ImperialCollegeLondon/openFrame/openFrame CAD/OF-PP-SM30.stp

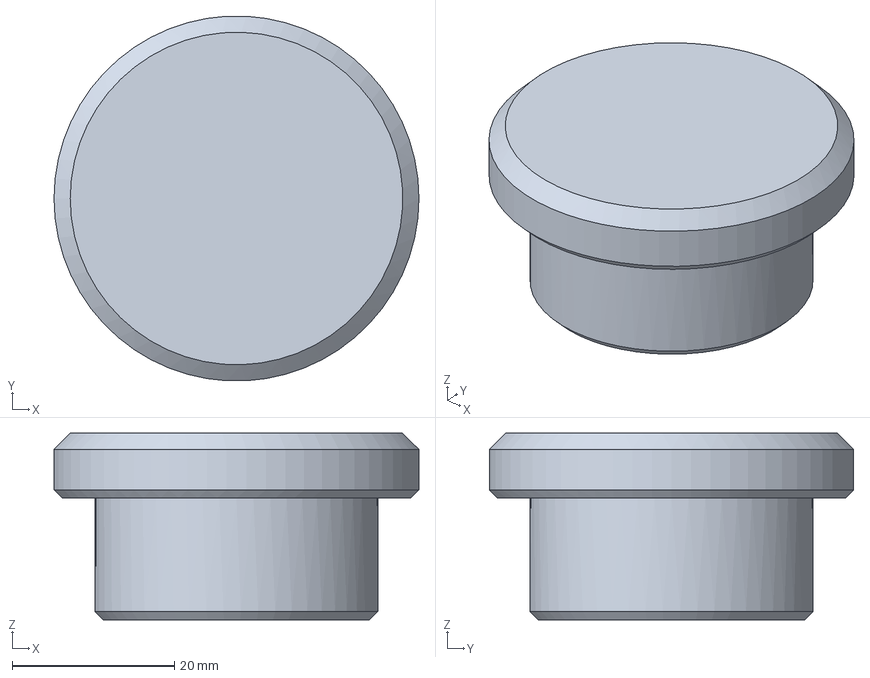
[picture p14: CAD file, 2023-07-18]
openFrame CAD/OF-PP-SM30.stp
45.0 x 44.9 x 23.0 mm
