ImperialCollegeLondon/openFrame/openFrame CAD/OF-AD-TI-ARM-LED-CAIRN.stp

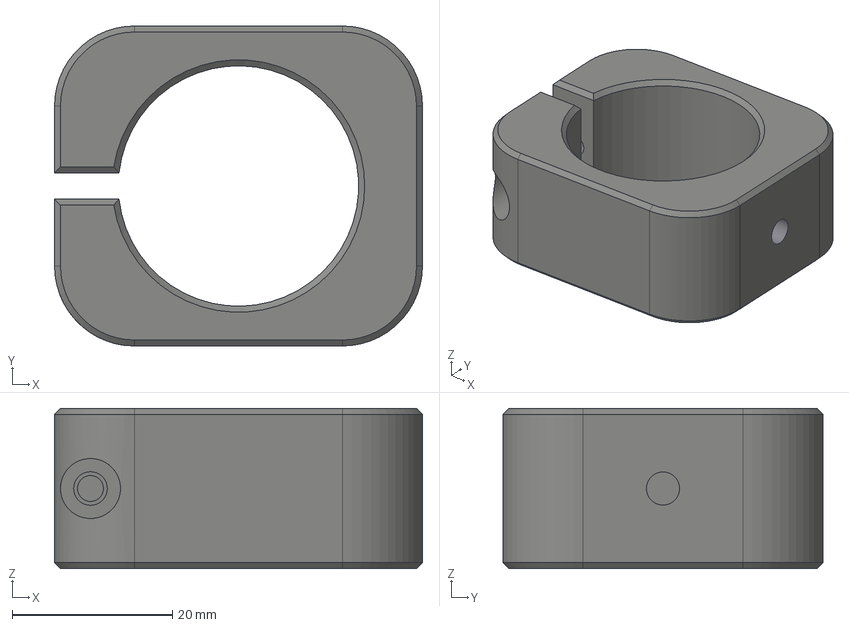
[picture p15: CAD file, 2023-07-18]
openFrame CAD/OF-AD-TI-ARM-LED-CAIRN.stp
46.0 x 40.0 x 20.0 mm
