ImperialCollegeLondon/openFrame/openFrame CAD/OF-AD-SM2-TL-OLYMPUS.stp

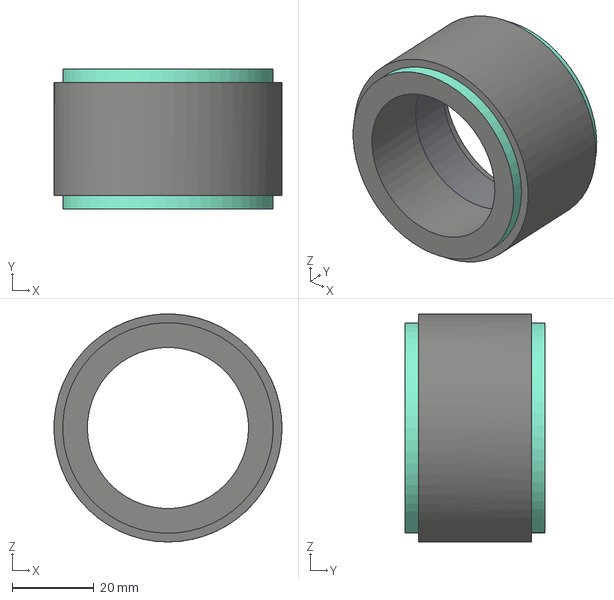
[picture p16: CAD file, 2023-07-18]
openFrame CAD/OF-AD-SM2-TL-OLYMPUS.stp
55.9 x 34.2 x 55.9 mm
