ImperialCollegeLondon/openFrame/openFrame CAD/OF-AD-LL-SM1.stp

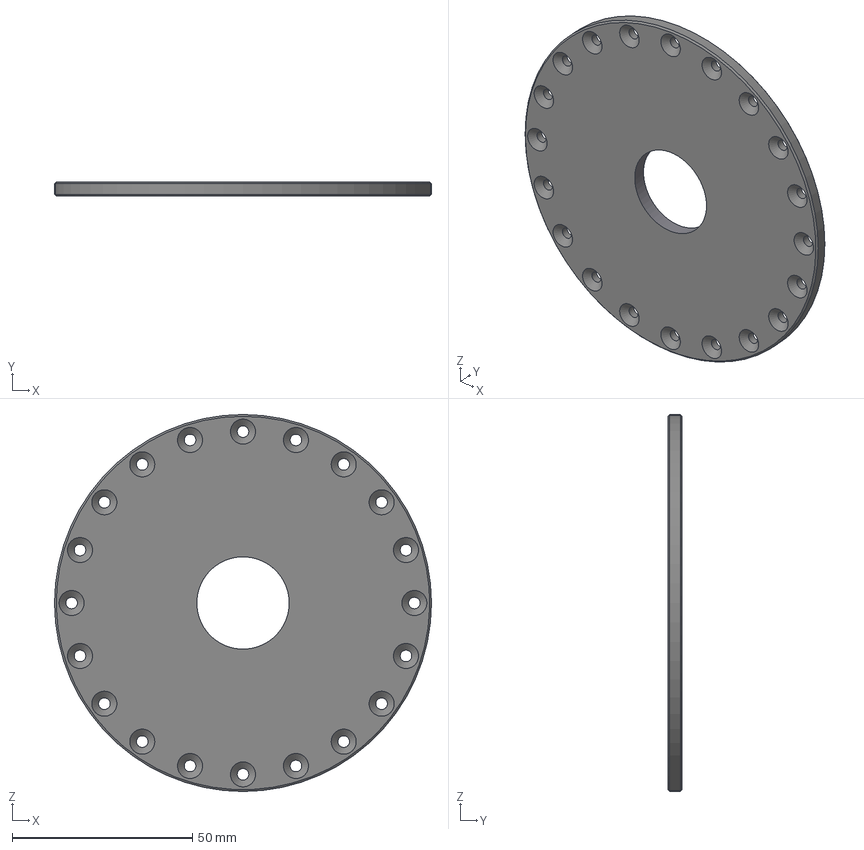
[picture p17: CAD file, 2023-07-18]
openFrame CAD/OF-AD-LL-SM1.stp
104.5 x 4.00 x 104.5 mm
