ImperialCollegeLondon/openFrame/openFrame CAD/OF-CL-SM2.stp

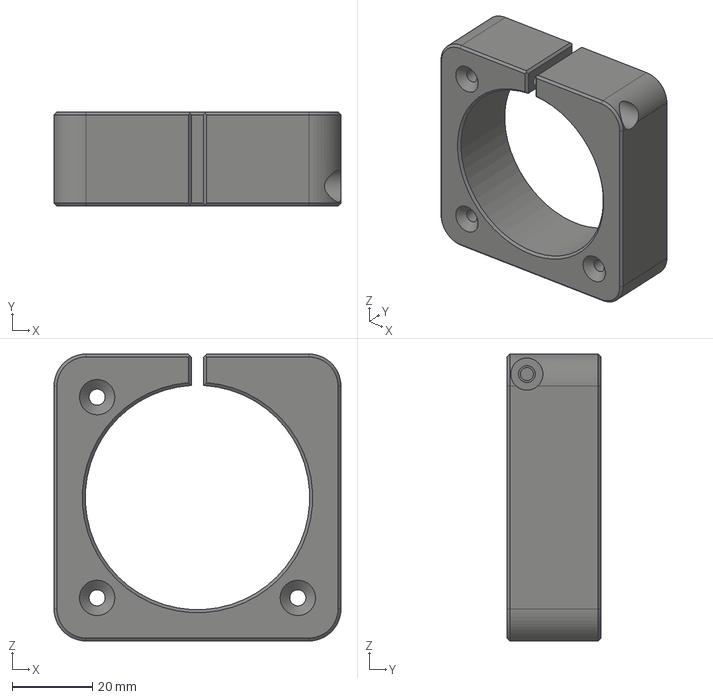
[picture p18: CAD file, 2023-07-18]
openFrame CAD/OF-CL-SM2.stp
71.5 x 23.5 x 71.5 mm
