ImperialCollegeLondon/openFrame/openFrame CAD/OF-PP-SM2.stp

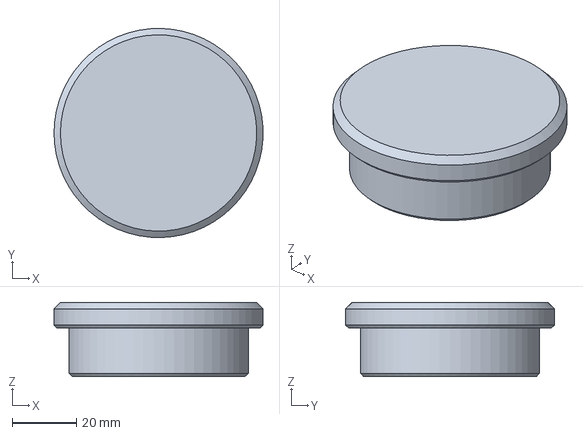
[picture p19: CAD file, 2023-07-18]
openFrame CAD/OF-PP-SM2.stp
65.0 x 65.0 x 23.0 mm
