ImperialCollegeLondon/openFrame/openFrame CAD/OF-LL-FL-MOT.stp

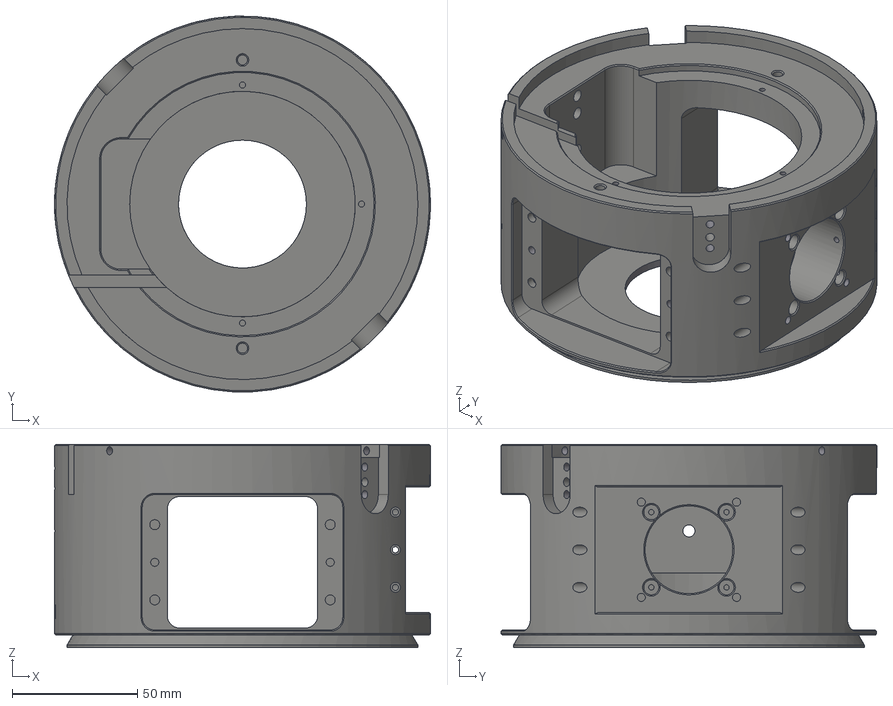
[picture p20: CAD file, 2023-07-18]
openFrame CAD/OF-LL-FL-MOT.stp
150.0 x 149.9 x 81.0 mm
