ImperialCollegeLondon/openFrame/openFrame CAD/OF-AD-OBH-RMS-45.stp

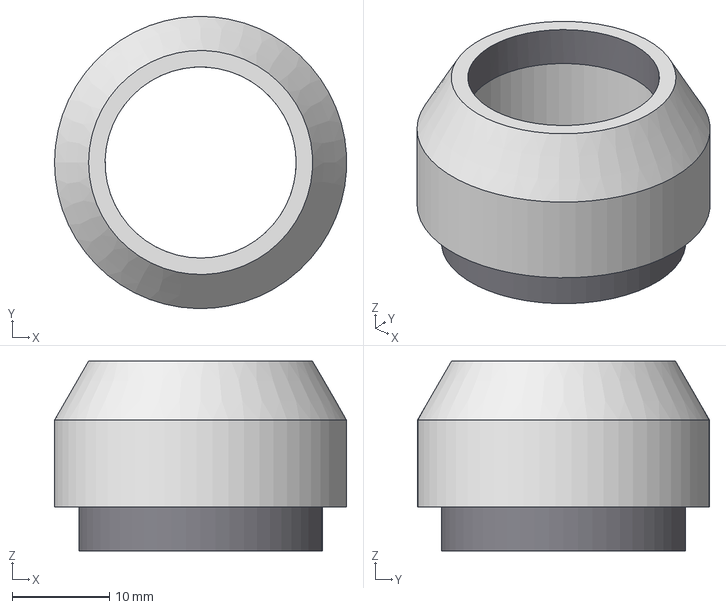
[picture p21: CAD file, 2023-07-18]
openFrame CAD/OF-AD-OBH-RMS-45.stp
30.0 x 30.0 x 19.5 mm
