ImperialCollegeLondon/openFrame/openFrame CAD/OF-LL-80.stp

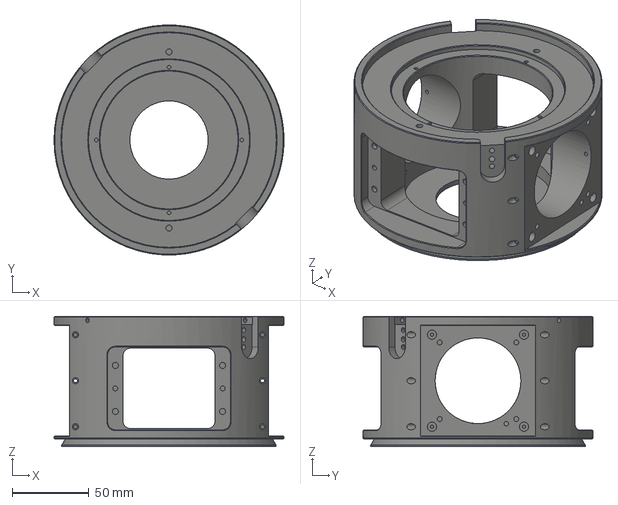
[picture p22: CAD file, 2023-07-18]
openFrame CAD/OF-LL-80.stp
150.0 x 149.9 x 85.0 mm
