ImperialCollegeLondon/openFrame/openFrame CAD/OF-IN-2P-OD.stp

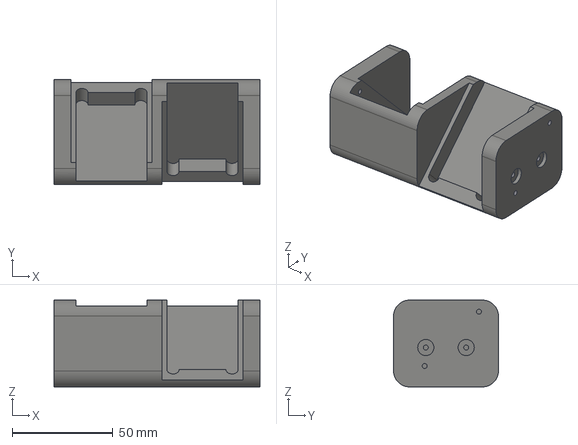
[picture p23: CAD file, 2023-07-18]
openFrame CAD/OF-IN-2P-OD.stp
102.0 x 52.0 x 43.0 mm
