ImperialCollegeLondon/openFrame/openFrame CAD/OF-AD-SBSM2-CM.stp

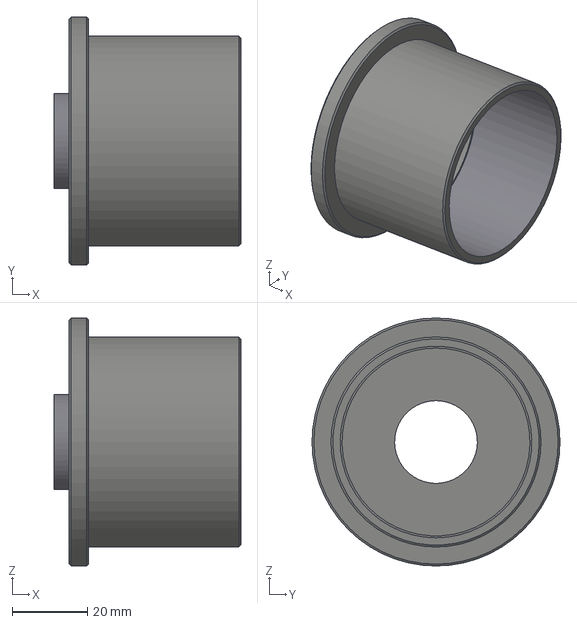
[picture p24: CAD file, 2023-07-18]
openFrame CAD/OF-AD-SBSM2-CM.stp
49.6 x 66.0 x 66.0 mm
