ImperialCollegeLondon/openFrame/openFrame CAD/OF-CL-LC.stp

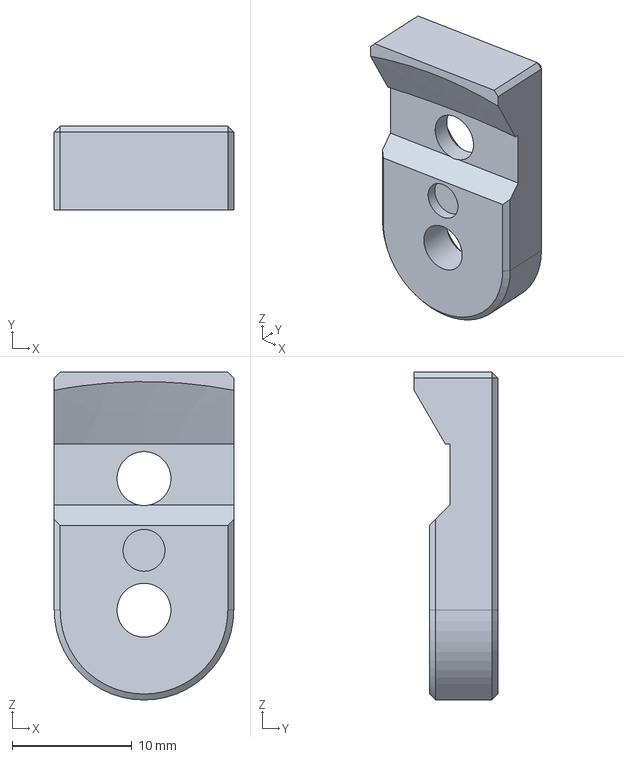
[picture p25: CAD file, 2023-07-18]
openFrame CAD/OF-CL-LC.stp
15.0 x 7.00 x 27.4 mm
