ImperialCollegeLondon/openFrame/openFrame CAD/OF-HA-2P-OD.stp

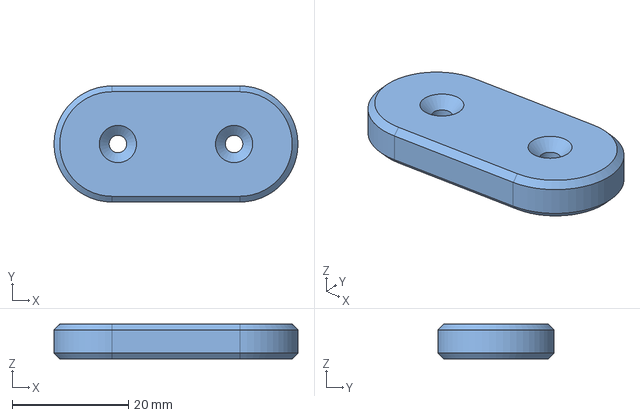
[picture p26: CAD file, 2023-07-18]
openFrame CAD/OF-HA-2P-OD.stp
42.0 x 20.0 x 6.00 mm
