ImperialCollegeLondon/openFrame/openFrame CAD/OF-LL-65.stp

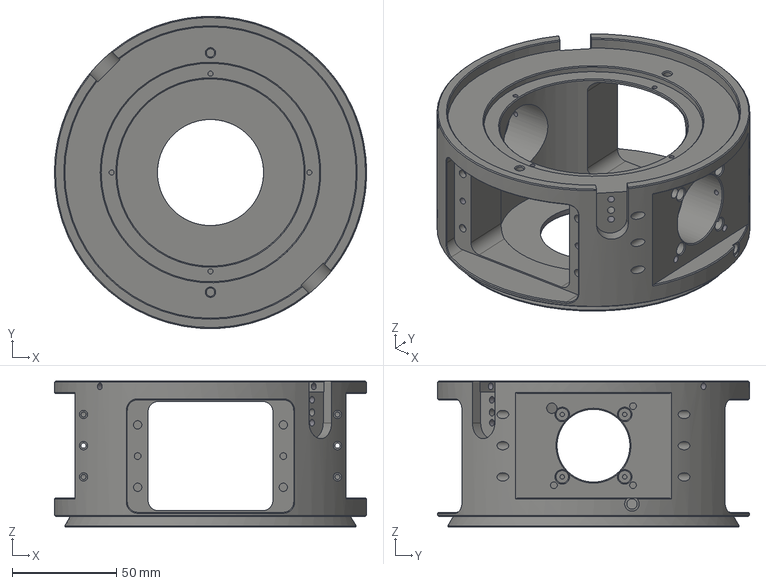
[picture p27: CAD file, 2023-07-18]
openFrame CAD/OF-LL-65.stp
150.0 x 149.9 x 70.0 mm
