ImperialCollegeLondon/openFrame/openFrame CAD/OF-AD-FL-PZ-PI-Q545.stp

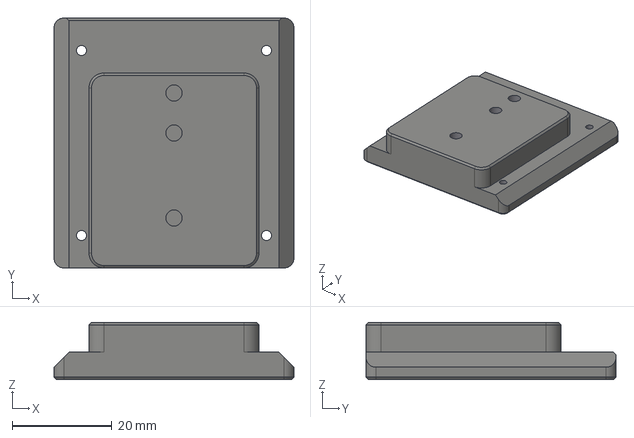
[picture p28: CAD file, 2023-07-18]
openFrame CAD/OF-AD-FL-PZ-PI-Q545.stp
48.0 x 50.0 x 11.5 mm
