ImperialCollegeLondon/openFrame/openFrame CAD/OF-CL-SM30.stp

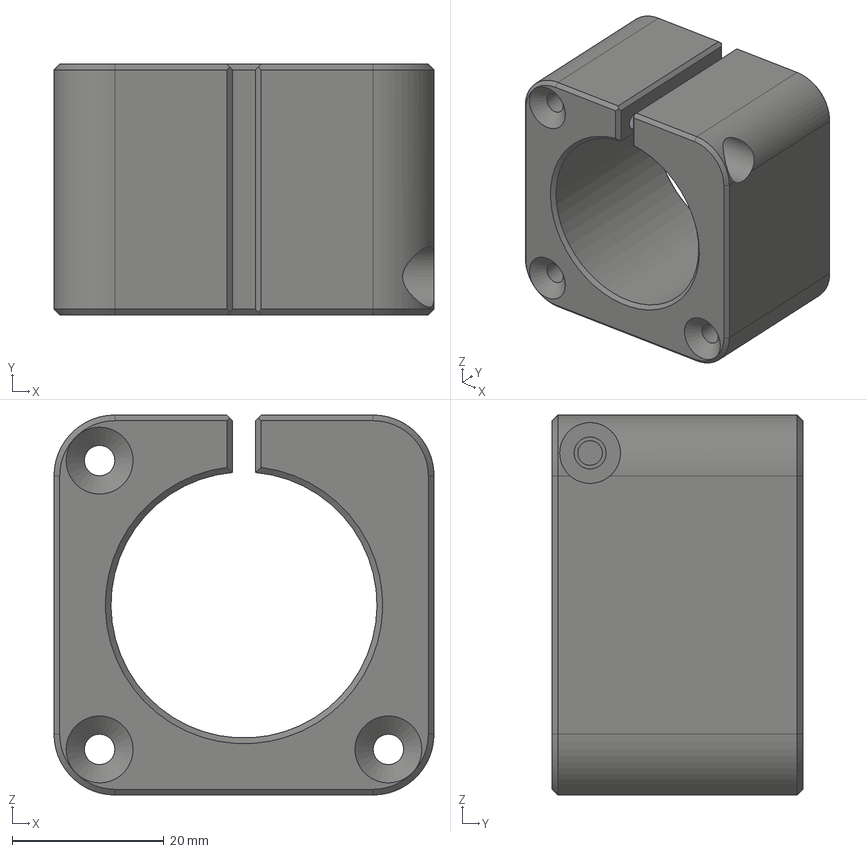
[picture p29: CAD file, 2023-07-18]
openFrame CAD/OF-CL-SM30.stp
50.0 x 33.0 x 50.0 mm
