ImperialCollegeLondon/openFrame/openFrame CAD/OF-AD-HA-IN-2P-OD.stp

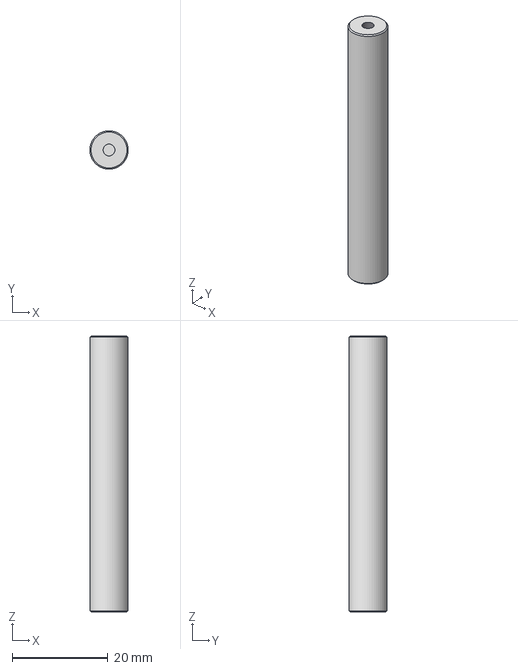
[picture p30: CAD file, 2023-07-18]
openFrame CAD/OF-AD-HA-IN-2P-OD.stp
7.99 x 8.00 x 57.5 mm
