ImperialCollegeLondon/openFrame/openFrame CAD/OF-AC-2P-OD.stp

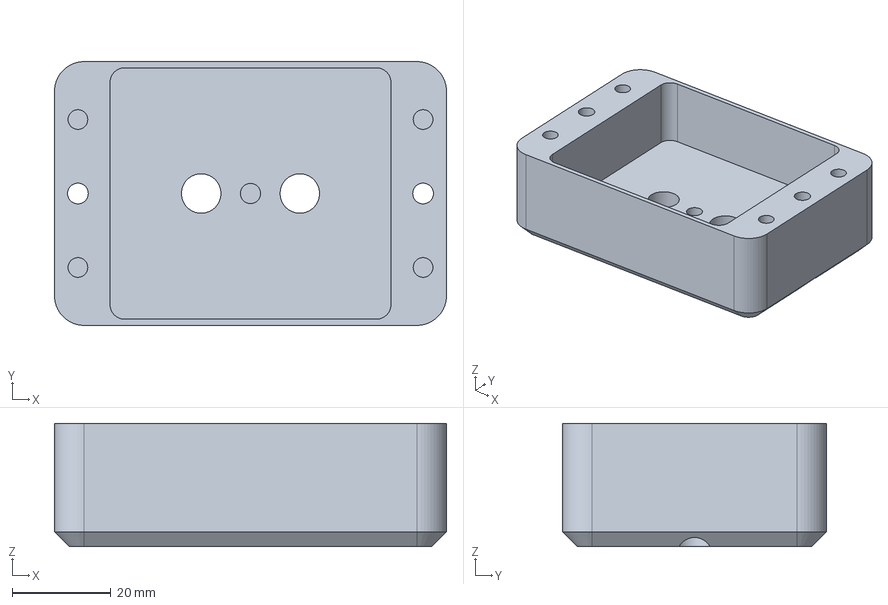
[picture p31: CAD file, 2023-07-18]
openFrame CAD/OF-AC-2P-OD.stp
79.5 x 53.5 x 25.0 mm
