ImperialCollegeLondon/openFrame/openFrame CAD/OF-TI-ARM.step

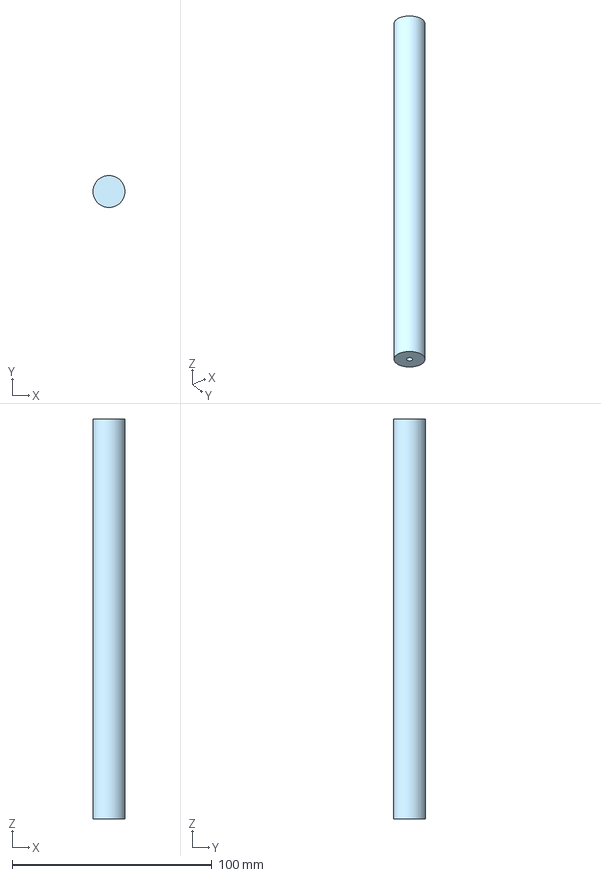
[picture p32: CAD file, 2023-06-29]
openFrame CAD/OF-TI-ARM.step
16.0 x 16.0 x 200.0 mm
