ImperialCollegeLondon/openFrame/openFrame CAD/OF-TI-PILLAR.step

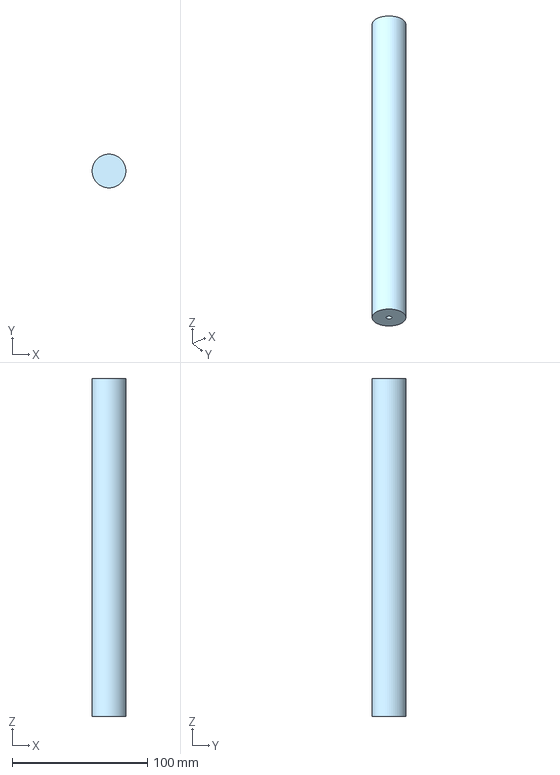
[picture p33: CAD file, 2023-06-29]
openFrame CAD/OF-TI-PILLAR.step
25.0 x 25.0 x 250.0 mm
