ImperialCollegeLondon/openFrame/openFrame part description PDFs/OF-AD-LL-SM1.pdf

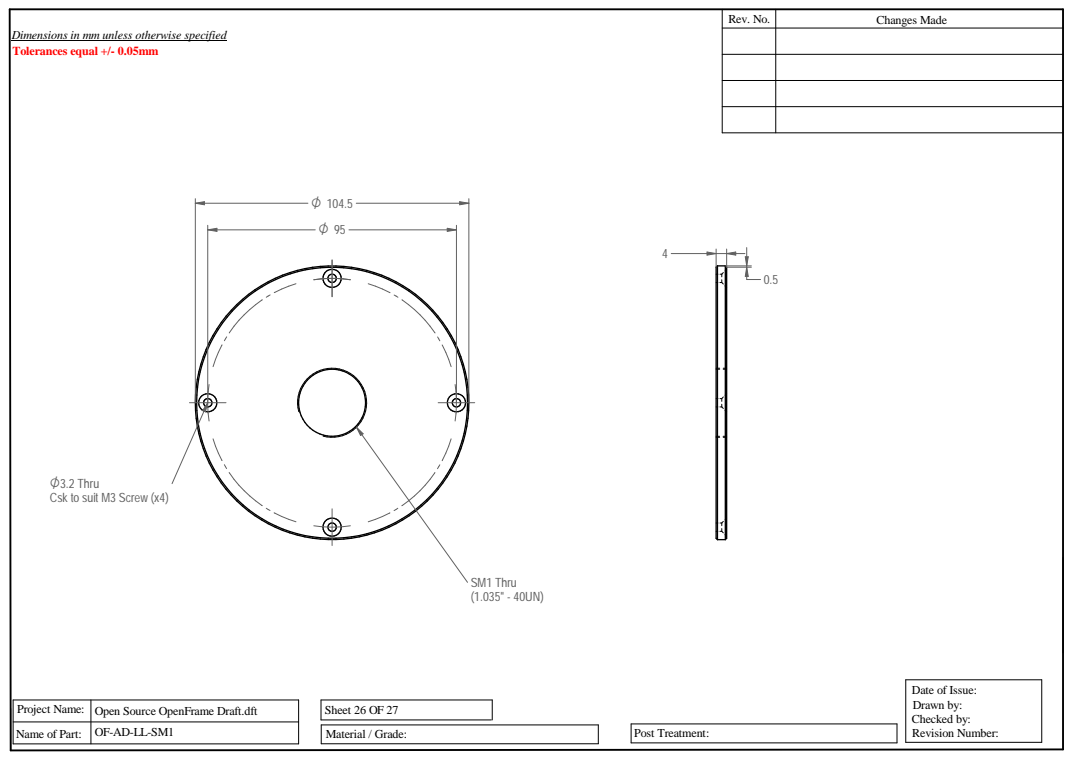
[picture p42: page 1]
Project Name:; Material / Grade:; Post Treatment:; Open Source OpenFrame Draft.dft; Sheet 26 OF 27; Rev. No.; Changes Made; SM1 Thru (1.035" - 40UN)

Dimensions in mm unless otherwise specified
Tolerances equal +/- 0.05mm

O3.2 Thru
Csk to suit M3 Screw (x4)

Date of Issue:
Drawn by:
Checked by:
Revision Number:

Name of Part:
