ImperialCollegeLondon/openFrame/openFrame part description PDFs/OF-AD-MCH-M45.pdf

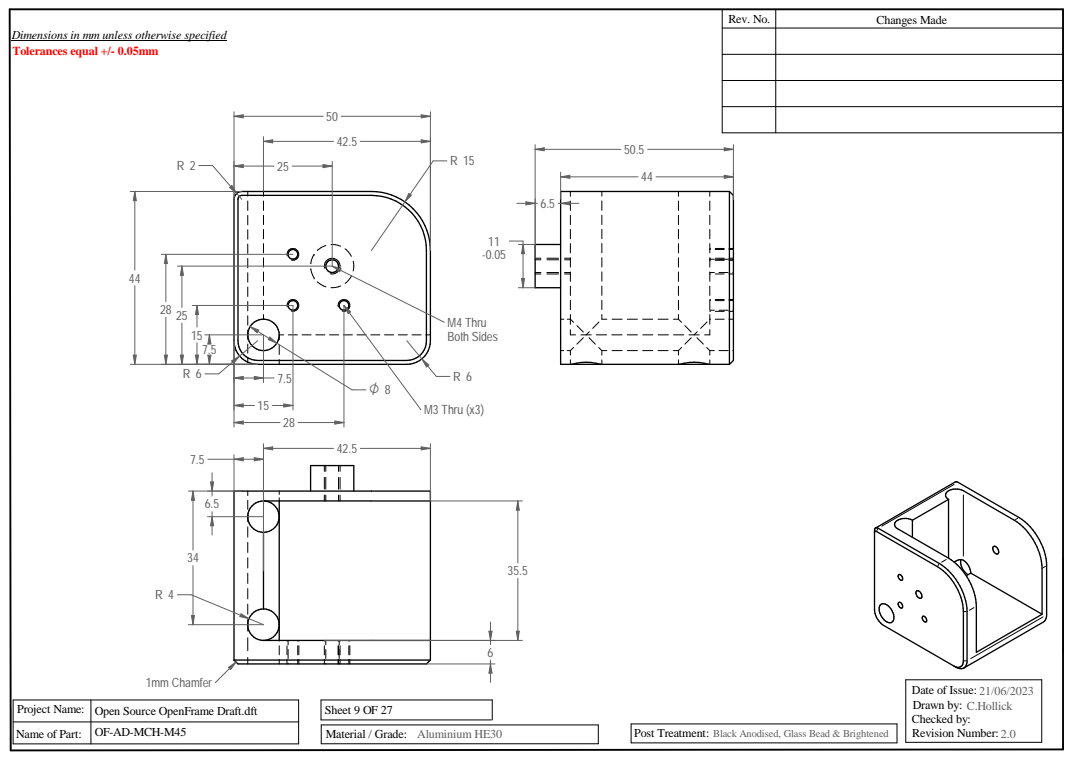
[picture p43: page 1]
Project Name:; OF-AD-MCH-M45; Material / Grade:; Post Treatment:; Open Source OpenFrame Draft.dft; Sheet 9 OF 27; Rev. No.; Changes Made; M3 Thru (x3); M4 Thru Both Sides; 1mm Chamfer; Aluminium HE30; Black Anodised, Glass Bead & Brightened; C.Hollick

Dimensions in mm unless otherwise specified
Tolerances equal +/- 0.05mm

Date of Issue:
Drawn by:
Checked by:
Revision Number:

Name of Part:
