ImperialCollegeLondon/openFrame/openFrame part description PDFs/OF-AD-PZ-PI-Q545-OBH.pdf

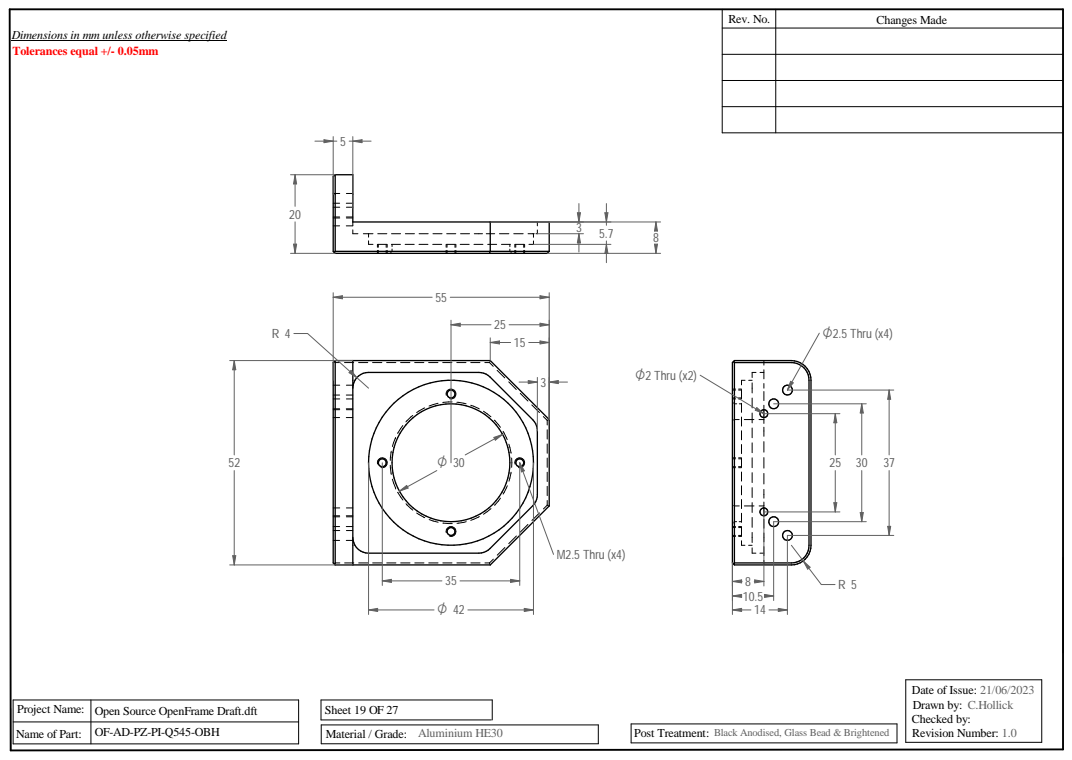
[picture p44: page 1]
Project Name:; OF-AD-PZ-PI-Q545-OBH; Material / Grade:; Post Treatment:; Open Source OpenFrame Draft.dft; Sheet 19 OF 27; Rev. No.; Changes Made; Aluminium HE30; Black Anodised, Glass Bead & Brightened; C.Hollick; M2.5 Thru (x4); O2 Thru (x2); O2.5 Thru (x4)

Dimensions in mm unless otherwise specified
Tolerances equal +/- 0.05mm

Date of Issue:
Drawn by:
Checked by:
Revision Number:

Name of Part:
