ImperialCollegeLondon/openFrame/openFrame part description PDFs/OF-AD-SBSM2-CM.pdf

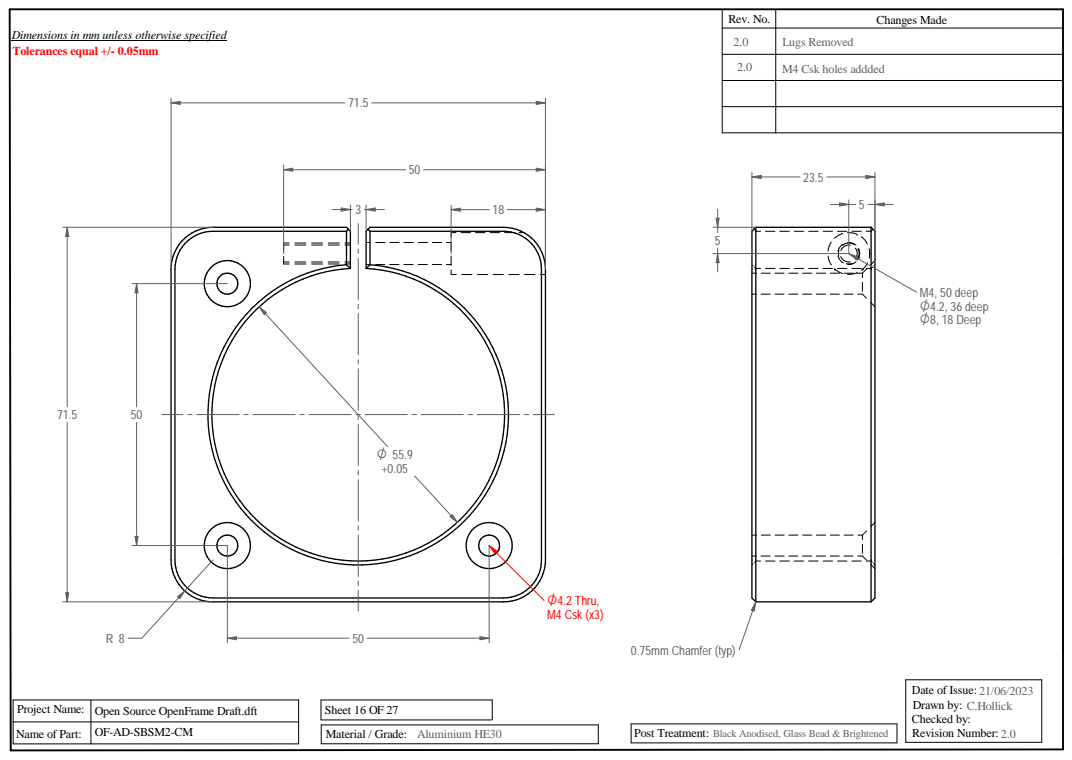
[picture p45: page 1]
Project Name:; Tolerances equal +/- 0.05mm; OF-AD-SBSM2-CM; Material / Grade:; Post Treatment:; Open Source OpenFrame Draft.dft; Sheet 16 OF 27; 0.75mm Chamfer (typ); Aluminium HE30; Black Anodised, Glass Bead & Brightened; C.Hollick; O4.2 Thru, M4 Csk (x3)

Dimensions in mm unless otherwise specified | Rev. No. | Changes Made

2.0 | Lugs Removed

2.0 | M4 Csk holes addded

M4, 50 deep O4.2, 36 deep O8, 18 Deep

Date of Issue:
Drawn by:
Checked by:
Revision Number:

Name of Part:
