ImperialCollegeLondon/openFrame/openFrame part description PDFs/OF-AD-SBSM30-CM.pdf

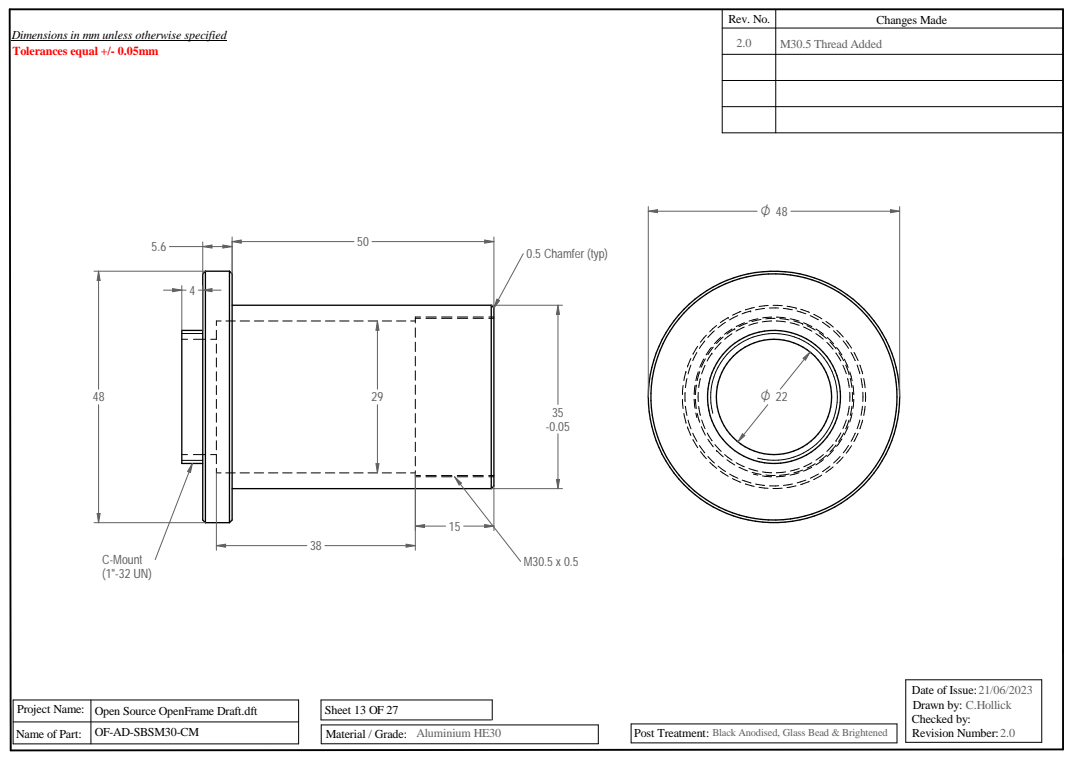
[picture p46: page 1]
Project Name:; OF-AD-SBSM30-CM; Material / Grade:; Post Treatment:; Open Source OpenFrame Draft.dft; Sheet 13 OF 27; C-Mount (1"-32 UN); Aluminium HE30; Black Anodised, Glass Bead & Brightened; C.Hollick; 0.5 Chamfer (typ)

Rev. No. | Changes Made

Dimensions in mm unless otherwise specified
Tolerances equal +/- 0.05mm

2.0 | M30.5 Thread Added

Date of Issue:
Drawn by:
Checked by:
Revision Number:

Name of Part:
