ImperialCollegeLondon/openFrame/openFrame part description PDFs/OF-AD-SM2-TL-NIKON.pdf

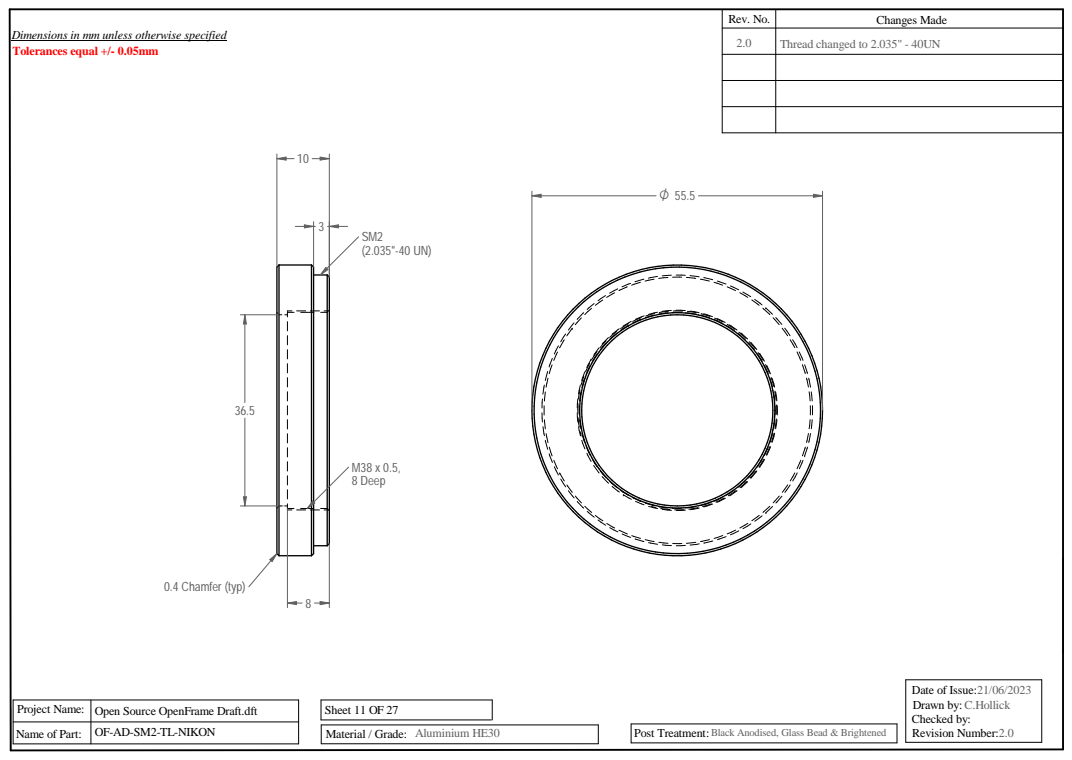
[picture p47: page 1]
Project Name:; OF-AD-SM2-TL-NIKON; Material / Grade:; Post Treatment:; Open Source OpenFrame Draft.dft; Sheet 11 OF 27; M38 x 0.5, 8 Deep; 0.4 Chamfer (typ); Aluminium HE30; Black Anodised, Glass Bead & Brightened; C.Hollick

Rev. No. | Changes Made

Dimensions in mm unless otherwise specified
Tolerances equal +/- 0.05mm

2.0 | Thread changed to 2.035" - 40UN

Date of Issue:
Drawn by:
Checked by:
Revision Number:

Name of Part:
