ImperialCollegeLondon/openFrame/openFrame part description PDFs/OF-AD-SM2-TL-OLYMPUS.pdf

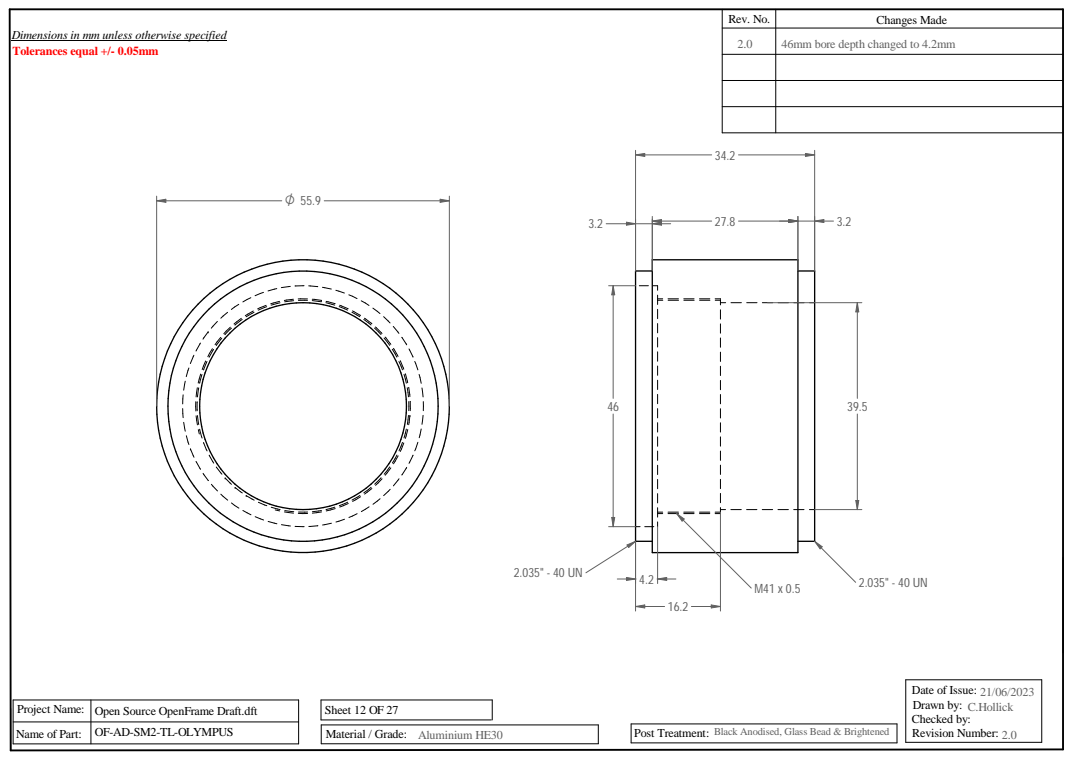
[picture p48: page 1]
Project Name:; OF-AD-SM2-TL-OLYMPUS; Material / Grade:; Post Treatment:; Open Source OpenFrame Draft.dft; Sheet 12 OF 27; Aluminium HE30; Black Anodised, Glass Bead & Brightened; C.Hollick

Rev. No. | Changes Made

Dimensions in mm unless otherwise specified
Tolerances equal +/- 0.05mm

2.0 | 46mm bore depth changed to 4.2mm

Date of Issue:
Drawn by:
Checked by:
Revision Number:

Name of Part:
