ImperialCollegeLondon/openFrame/openFrame part description PDFs/OF-AD-SP-TI-PILLAR.pdf

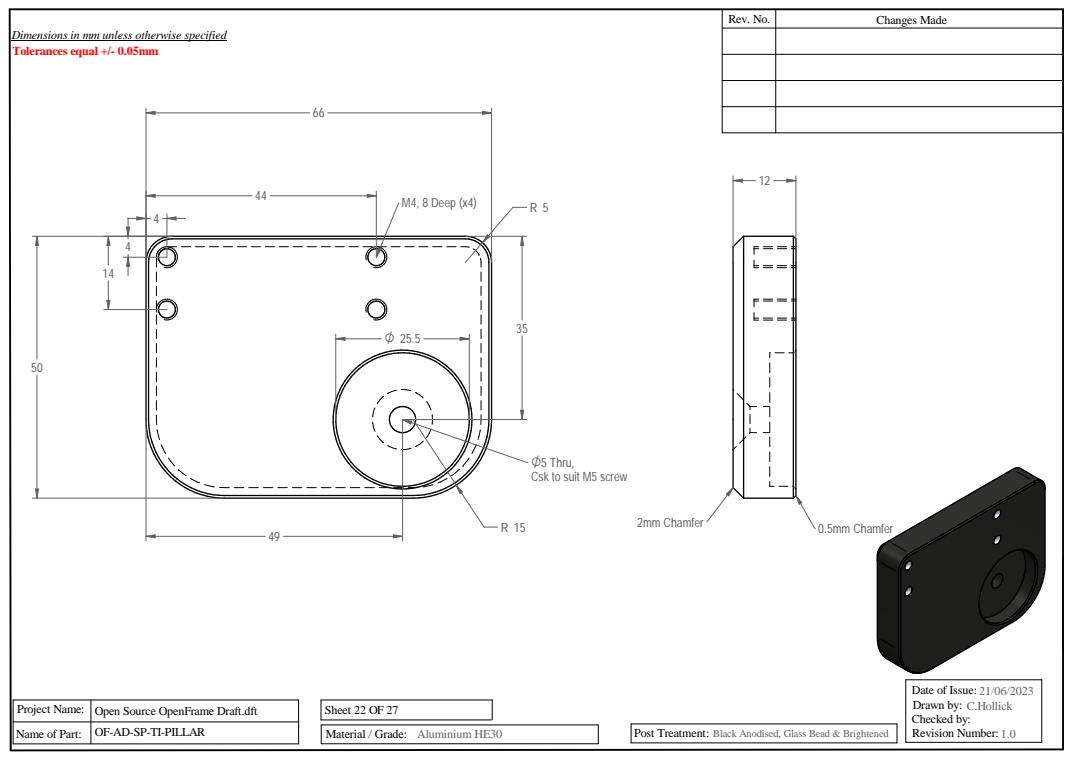
[picture p49: page 1]
Project Name:; OF-AD-SP-TI-PILLAR; Material / Grade:; Post Treatment:; Open Source OpenFrame Draft.dft; Sheet 22 OF 27; Rev. No.; Changes Made; Aluminium HE30; Black Anodised, Glass Bead & Brightened; C.Hollick; M4, 8 Deep (x4); 2mm Chamfer; 0.5mm Chamfer

Dimensions in mm unless otherwise specified
Tolerances equal +/- 0.05mm

O5 Thru,
Csk to suit M5 screw

Date of Issue:
Drawn by:
Checked by:
Revision Number:

Name of Part:
