ImperialCollegeLondon/openFrame/openFrame part description PDFs/OF-AD-SP-ZAB-PZ-PI-Q545.pdf

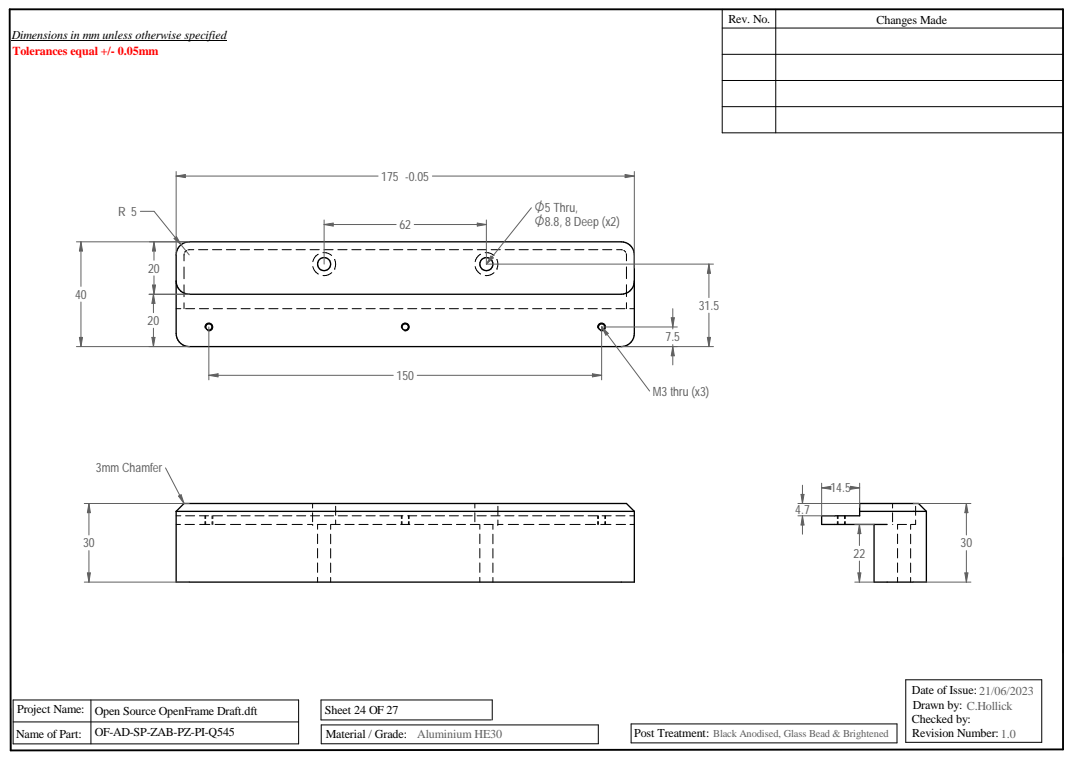
[picture p50: page 1]
Project Name:; OF-AD-SP-ZAB-PZ-PI-Q545; Material / Grade:; Post Treatment:; Open Source OpenFrame Draft.dft; Sheet 24 OF 27; Rev. No.; Changes Made; Aluminium HE30; Black Anodised, Glass Bead & Brightened; C.Hollick; O5 Thru, O8.8, 8 Deep (x2); M3 thru (x3); 3mm Chamfer

Dimensions in mm unless otherwise specified
Tolerances equal +/- 0.05mm

Date of Issue:
Drawn by:
Checked by:
Revision Number:

Name of Part:
