ImperialCollegeLondon/openFrame/openFrame part description PDFs/OF-AD-TI-ARM-LED-CAIRN.pdf

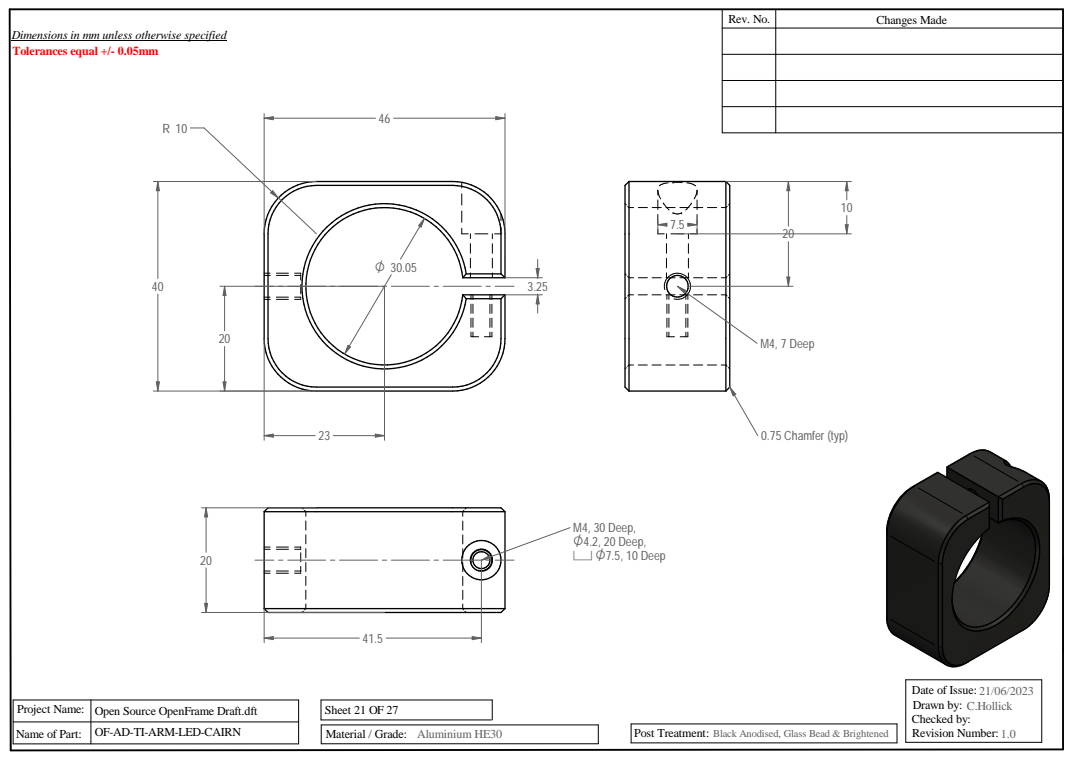
[picture p51: page 1]
Project Name:; OF-AD-TI-ARM-LED-CAIRN; Material / Grade:; Post Treatment:; Open Source OpenFrame Draft.dft; Sheet 21 OF 27; Rev. No.; Changes Made; Aluminium HE30; Black Anodised, Glass Bead & Brightened; C.Hollick; 0.75 Chamfer (typ); M4, 30 Deep, O4.2, 20 Deep,; cO7.5, 10 Deep; M4, 7 Deep

Dimensions in mm unless otherwise specified
Tolerances equal +/- 0.05mm

Date of Issue:
Drawn by:
Checked by:
Revision Number:

Name of Part:
