ImperialCollegeLondon/openFrame/openFrame part description PDFs/OF-AD-TI-PILLAR-TI-ARM.pdf

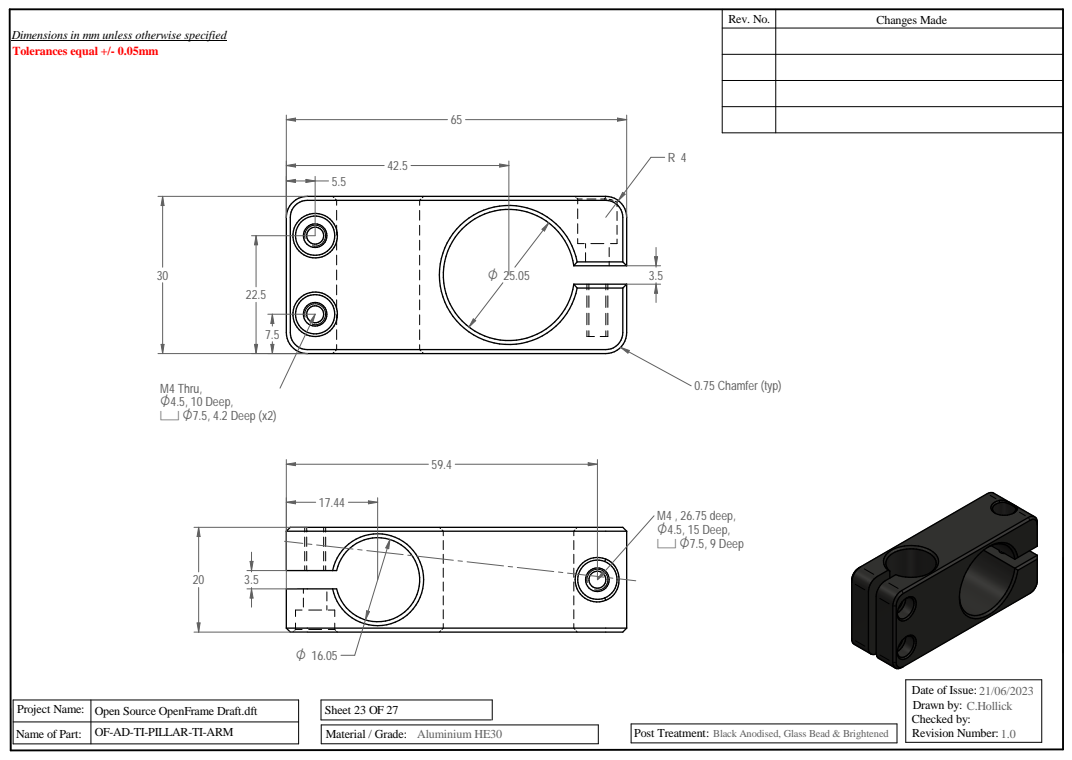
[picture p52: page 1]
Project Name:; OF-AD-TI-PILLAR-TI-ARM; Material / Grade:; Post Treatment:; Open Source OpenFrame Draft.dft; Sheet 23 OF 27; Rev. No.; Changes Made; Aluminium HE30; Black Anodised, Glass Bead & Brightened; C.Hollick; M4 Thru, O4.5, 10 Deep, cO7.5, 4.2 Deep (x2); M4 , 26.75 deep, O4.5, 15 Deep,; cO7.5, 9 Deep; 0.75 Chamfer (typ)

Dimensions in mm unless otherwise specified
Tolerances equal +/- 0.05mm

Date of Issue:
Drawn by:
Checked by:
Revision Number:

Name of Part:
