ImperialCollegeLondon/openFrame/openFrame part description PDFs/OF-CL-LC.pdf

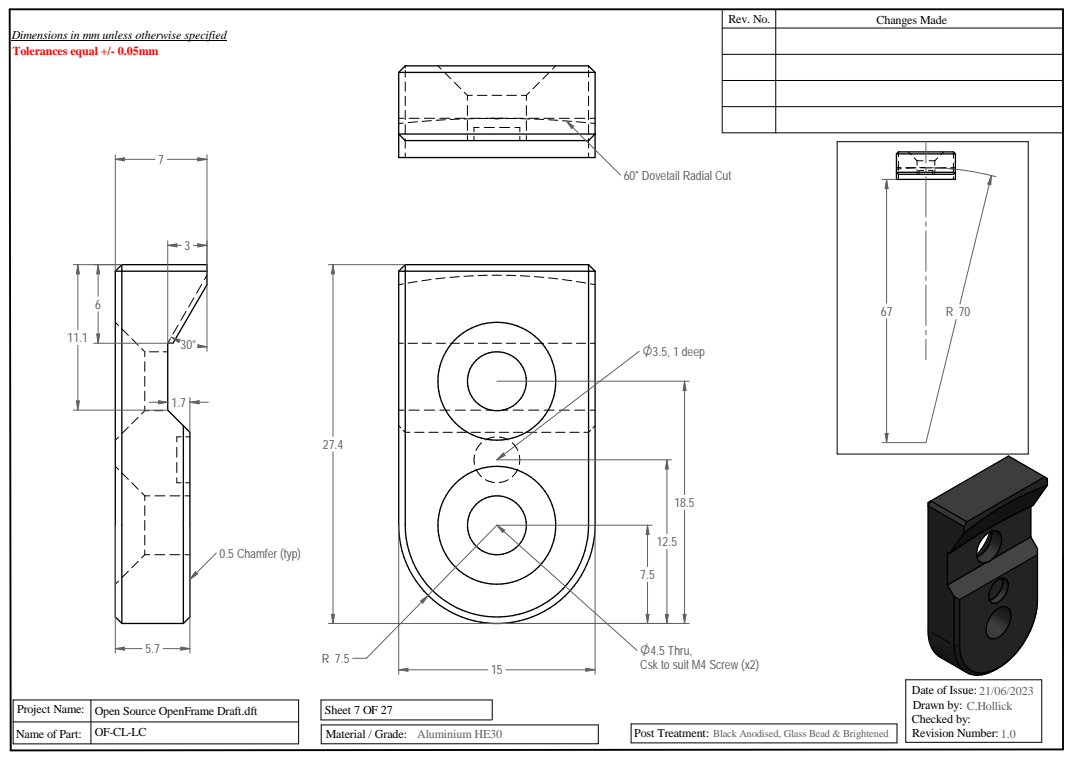
[picture p53: page 1]
Project Name:; Material / Grade:; Post Treatment:; Open Source OpenFrame Draft.dft; Sheet 7 OF 27; Rev. No.; Changes Made; 0.5 Chamfer (typ); O3.5, 1 deep; Aluminium HE30; Black Anodised, Glass Bead & Brightened; C.Hollick

Dimensions in mm unless otherwise specified
Tolerances equal +/- 0.05mm

60v Dovetail Radial Cut

O4.5 Thru,
Csk to suit M4 Screw (x2)

Date of Issue:
Drawn by:
Checked by:
Revision Number:

Name of Part:
