ImperialCollegeLondon/openFrame/openFrame part description PDFs/OF-CL-SM2.pdf

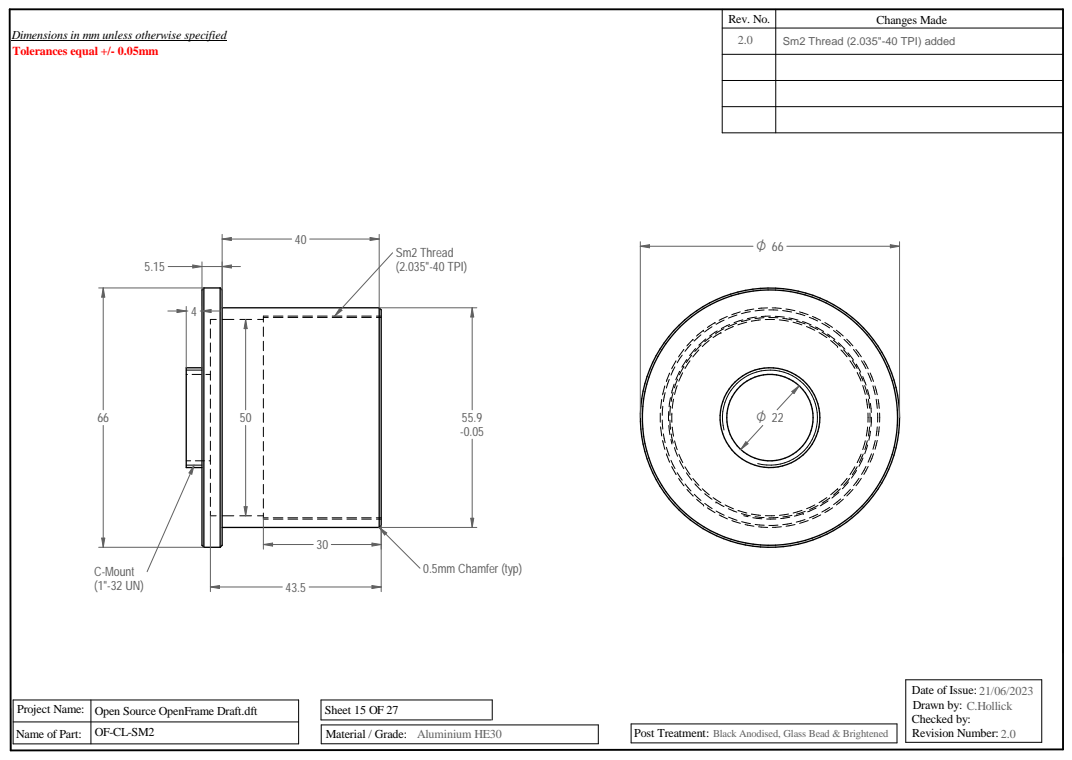
[picture p54: page 1]
Project Name:; Material / Grade:; Post Treatment:; Open Source OpenFrame Draft.dft; Sheet 15 OF 27; C-Mount (1"-32 UN); Aluminium HE30; Black Anodised, Glass Bead & Brightened; C.Hollick; 0.5mm Chamfer (typ); Sm2 Thread (2.035"-40 TPI)

Rev. No. | Changes Made

Dimensions in mm unless otherwise specified
Tolerances equal +/- 0.05mm

2.0 | Sm2 Thread (2.035"-40 TPI) added

Date of Issue:
Drawn by:
Checked by:
Revision Number:

Name of Part:
