ImperialCollegeLondon/openFrame/openFrame part description PDFs/OF-CL-SM30.pdf

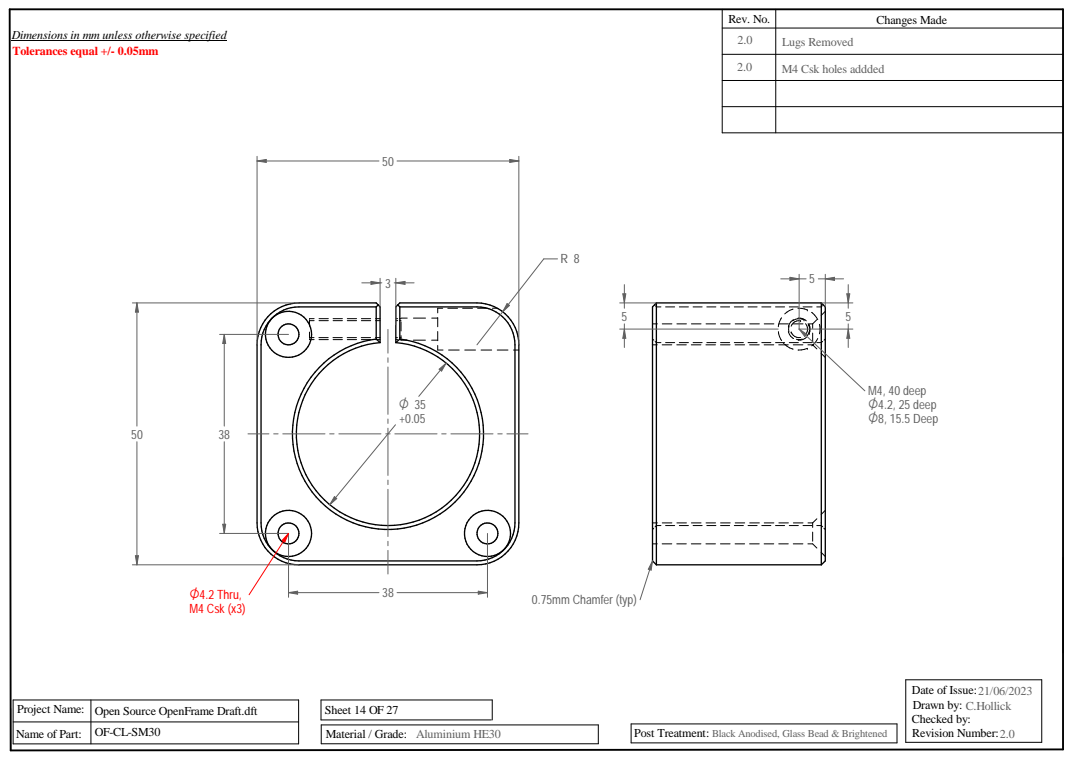
[picture p55: page 1]
Project Name:; Tolerances equal +/- 0.05mm; Material / Grade:; Post Treatment:; Open Source OpenFrame Draft.dft; Sheet 14 OF 27; Aluminium HE30; Black Anodised, Glass Bead & Brightened; C.Hollick; 0.75mm Chamfer (typ) 4.2 Thru, M4 Csk (x3)

Dimensions in mm unless otherwise specified | Rev. No. | Changes Made

2.0 | Lugs Removed

2.0 | M4 Csk holes addded

M4, 40 deep O4.2, 25 deep O8, 15.5 Deep

Date of Issue:
Drawn by:
Checked by:
Revision Number:

Name of Part:
