ImperialCollegeLondon/openFrame/openFrame part description PDFs/OF-IN-MCH.pdf

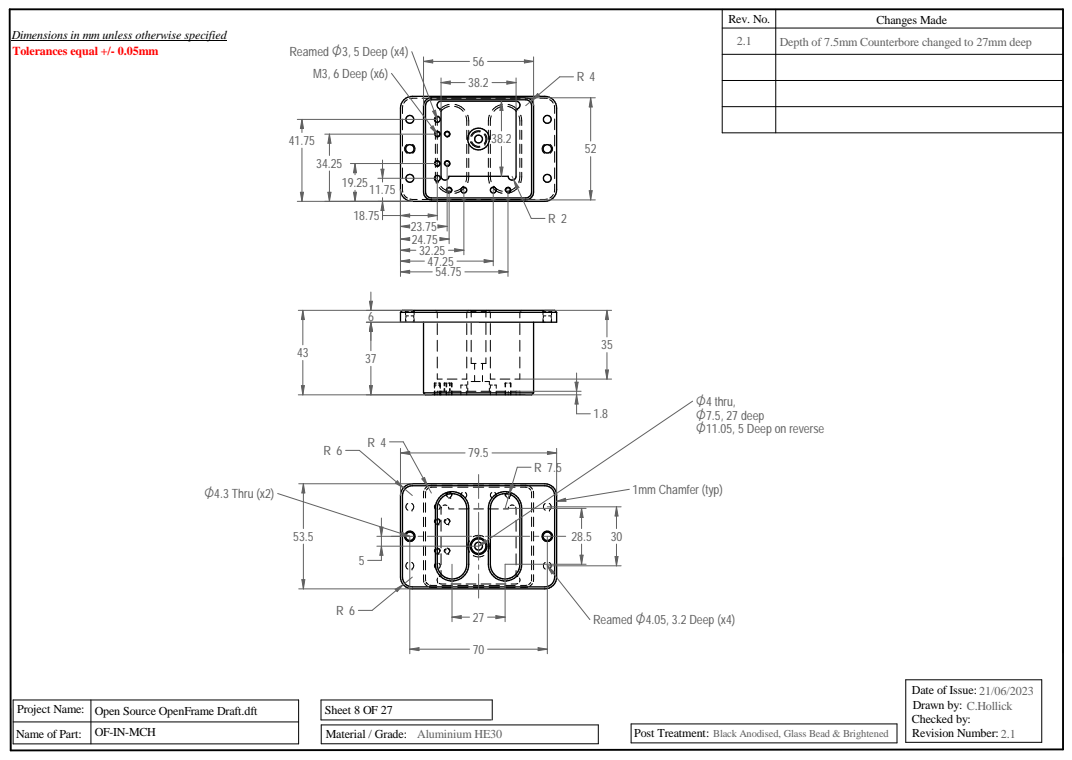
[picture p56: page 1]
Project Name:; OF-IN-MCH; Material / Grade:; Post Treatment:; Open Source OpenFrame Draft.dft; Sheet 8 OF 27; Reamed O4.05, 3.2 Deep (x4); O4.3 Thru (x2); Aluminium HE30; Black Anodised, Glass Bead & Brightened; C.Hollick; M3, 6 Deep (x6); 1mm Chamfer (typ)

Reamed O3, 5 Deep (x4) | Rev. No. | Changes Made

Dimensions in mm unless otherwise specified
Tolerances equal +/- 0.05mm

2.1 | Depth of 7.5mm Counterbore changed to 27mm deep

O4 thru,
O7.5, 27 deep O11.05, 5 Deep on reverse

Date of Issue:
Drawn by:
Checked by:
Revision Number:

Name of Part:
