ImperialCollegeLondon/openFrame/openFrame part description PDFs/OF-LL-65.pdf

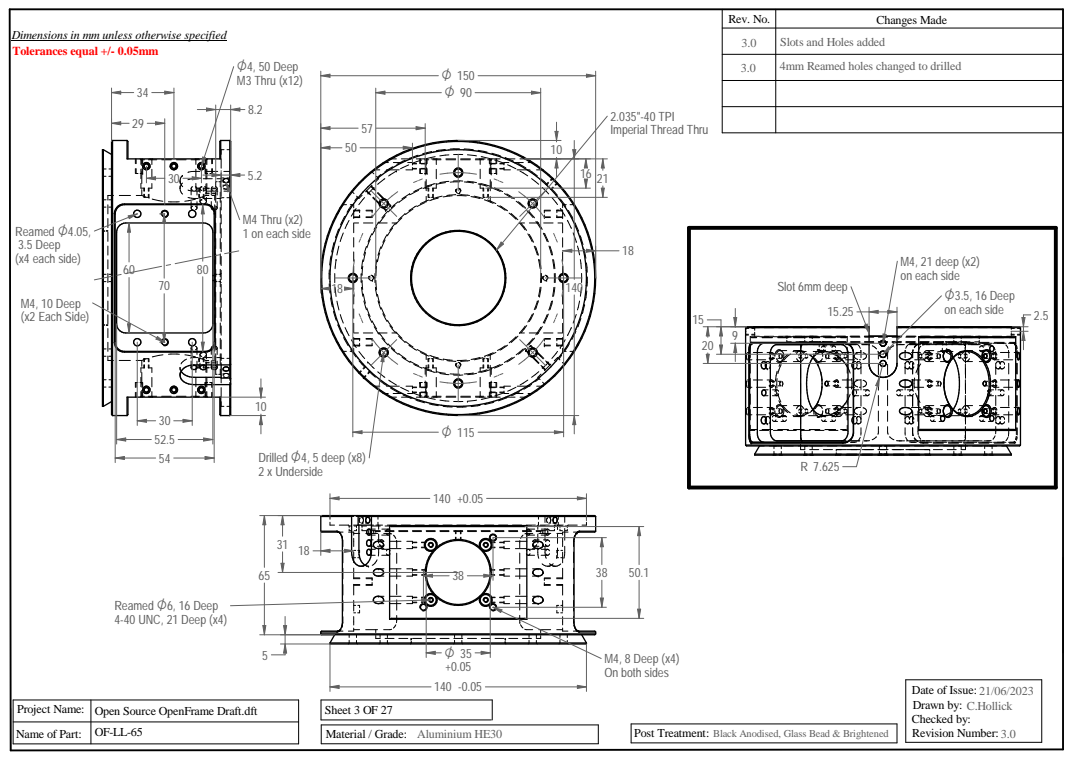
[picture p57: page 1]
Project Name:; Tolerances equal +/- 0.05mm; Material / Grade:; Post Treatment:; Open Source OpenFrame Draft.dft; Sheet 3 OF 27; O4, 50 Deep M3 Thru (x12); Aluminium HE30; Black Anodised, Glass Bead & Brightened; C.Hollick; Reamed O4.05, 3.5 Deep (x4 each side); M4, 10 Deep (x2 Each Side); Reamed O6, 16 Deep 4-40 UNC, 21 Deep (x4); Drilled O4, 5 deep (x8) 2 x Underside; Slot 6mm deep

Dimensions in mm unless otherwise specified | Rev. No. | Changes Made

3.0 | Slots and Holes added

3.0 | 4mm Reamed holes changed to drilled

2.035"-40 TPI
Imperial Thread Thru

M4 Thru (x2)
1 on each side

M4, 21 deep (x2)
on each side

O3.5, 16 Deep

M4, 8 Deep (x4)
On both sides

Date of Issue:
Drawn by:
Checked by:
Revision Number:

Name of Part:
