ImperialCollegeLondon/openFrame/openFrame part description PDFs/OF-LL-BP.pdf

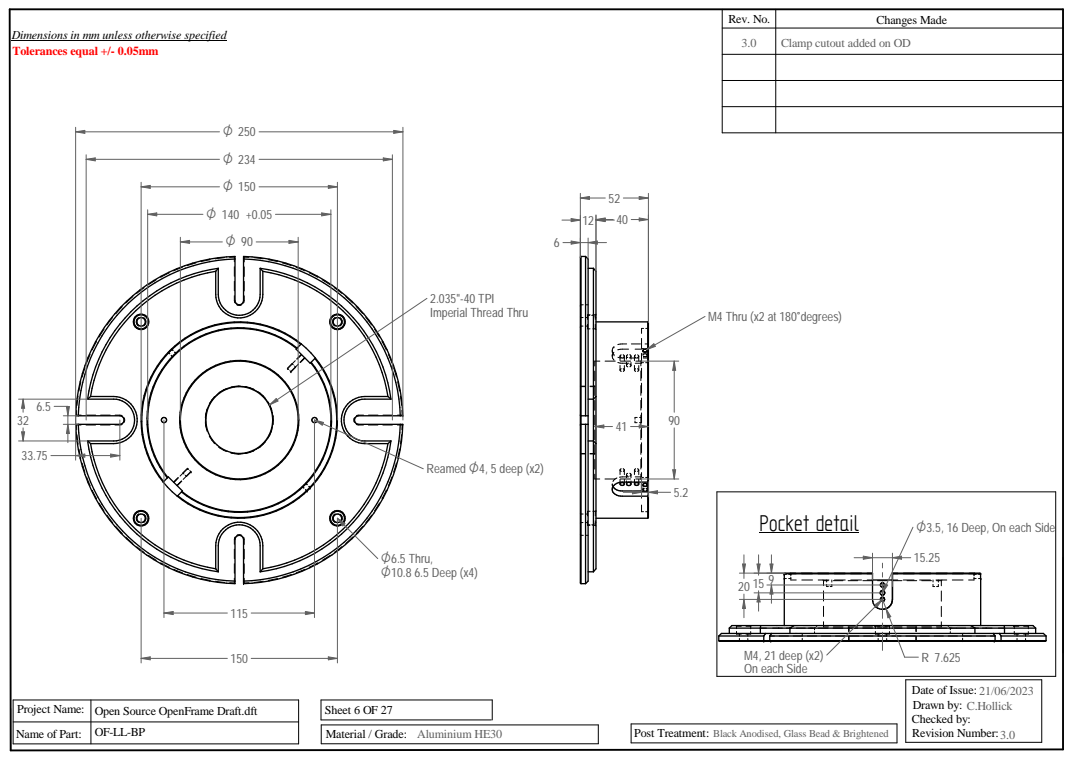
[picture p58: page 1]
Project Name:; Material / Grade:; Post Treatment:; Open Source OpenFrame Draft.dft; Sheet 6 OF 27; O6.5 Thru, O10.8 6.5 Deep (x4); Reamed O4, 5 deep (x2); Aluminium HE30; Black Anodised, Glass Bead & Brightened; C.Hollick; M4 Thru (x2 at 180vdegrees); Pocket detail

Dimensions in mm unless otherwise specified Tolerances equal +/- 0.05mm | Rev. No. | Changes Made

3.0 | Clamp cutout added on OD

2.035"-40 TPI
Imperial Thread Thru

O3.5, 16 Deep, On each Side

M4, 21 deep (x2)
On each Side

Date of Issue:
Drawn by:
Checked by:
Revision Number:

Name of Part:
