ImperialCollegeLondon/openFrame/openFrame part description PDFs/OF-LL-FL-MOT.pdf

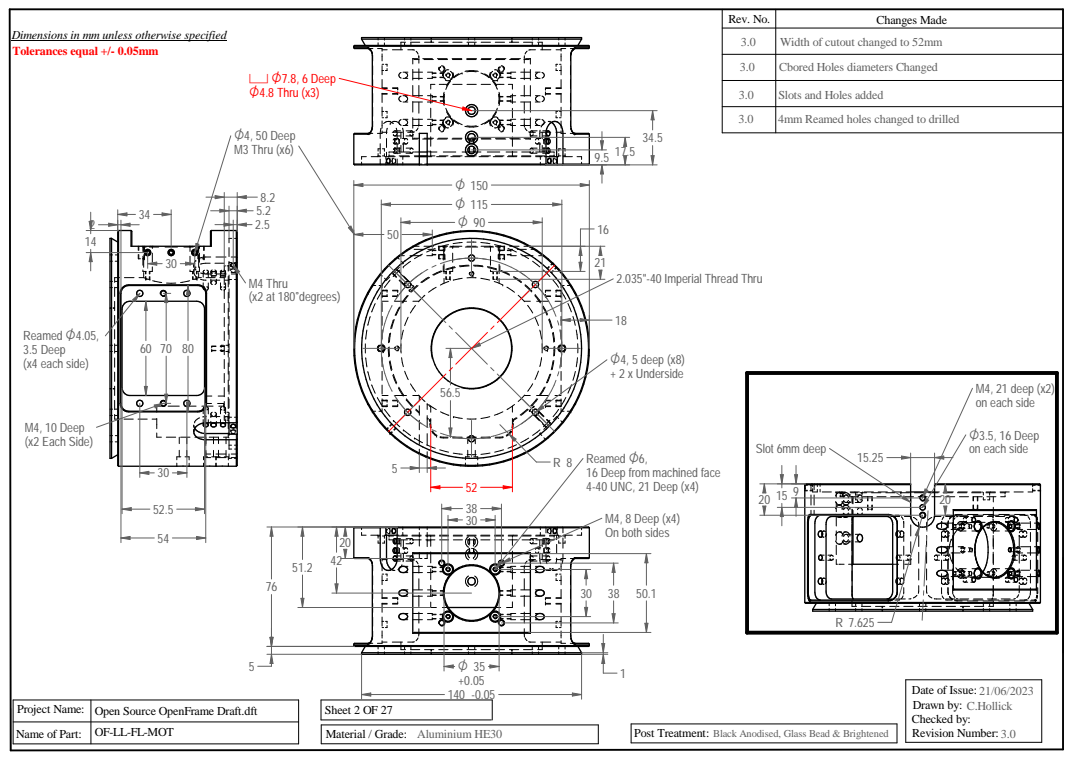
[picture p59: page 1]
Project Name:; Tolerances equal +/- 0.05mm; OF-LL-FL-MOT; Material / Grade:; Post Treatment:; Open Source OpenFrame Draft.dft; Sheet 2 OF 27; O4, 50 Deep M3 Thru (x6); O4, 5 deep (x8) + 2 x Underside; Aluminium HE30; Black Anodised, Glass Bead & Brightened; C.Hollick; Reamed O4.05, 3.5 Deep (x4 each side); M4, 10 Deep (x2 Each Side); cO7.8, 6 Deep O4.8 Thru (x3); Slot 6mm deep; M4 Thru (x2 at 180vdegrees)

Dimensions in mm unless otherwise specified | Rev. No. | Changes Made

3.0 | Width of cutout changed to 52mm

3.0 | Cbored Holes diameters Changed

3.0 | Slots and Holes added

3.0 | 4mm Reamed holes changed to drilled

2.035"-40 Imperial Thread Thru

M4, 21 deep (x2)
on each side

O3.5, 16 Deep

Reamed O6,
16 Deep from machined face
4-40 UNC, 21 Deep (x4)

M4, 8 Deep (x4)
On both sides

Date of Issue:
Drawn by:
Checked by:
Revision Number:

Name of Part:
