ImperialCollegeLondon/openFrame/openFrame part description PDFs/OF-LL-SP.pdf

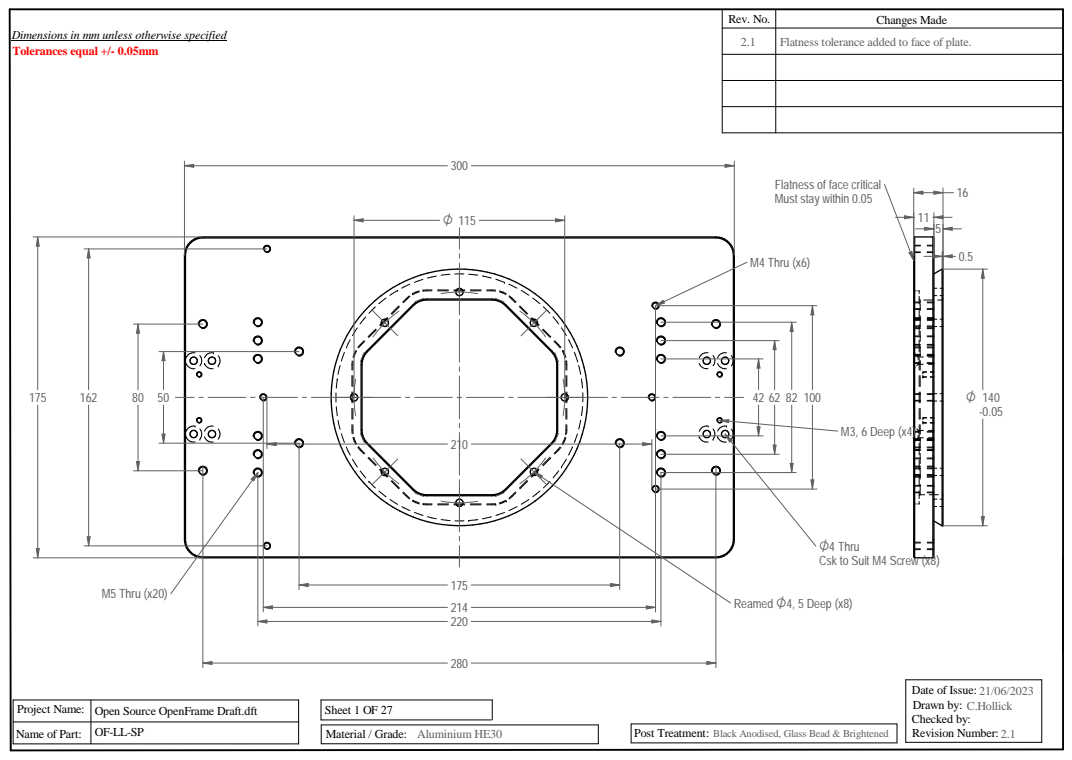
[picture p60: page 1]
Project Name:; Material / Grade:; Post Treatment:; Open Source OpenFrame Draft.dft; Sheet 1 OF 27; Aluminium HE30; Black Anodised, Glass Bead & Brightened; C.Hollick; Reamed O4, 5 Deep (x8); M4 Thru (x6); M3, 6 Deep (x4); M5 Thru (x20)

Rev. No. | Changes Made

Dimensions in mm unless otherwise specified
Tolerances equal +/- 0.05mm

2.1 | Flatness tolerance added to face of plate.

Flatness of face critical
Must stay within 0.05

O4 Thru
Csk to Suit M4 Screw (x8)

Date of Issue:
Drawn by:
Checked by:
Revision Number:

Name of Part:
