ImperialCollegeLondon/openFrame/openFrame part description PDFs/OF-LL-TL.pdf

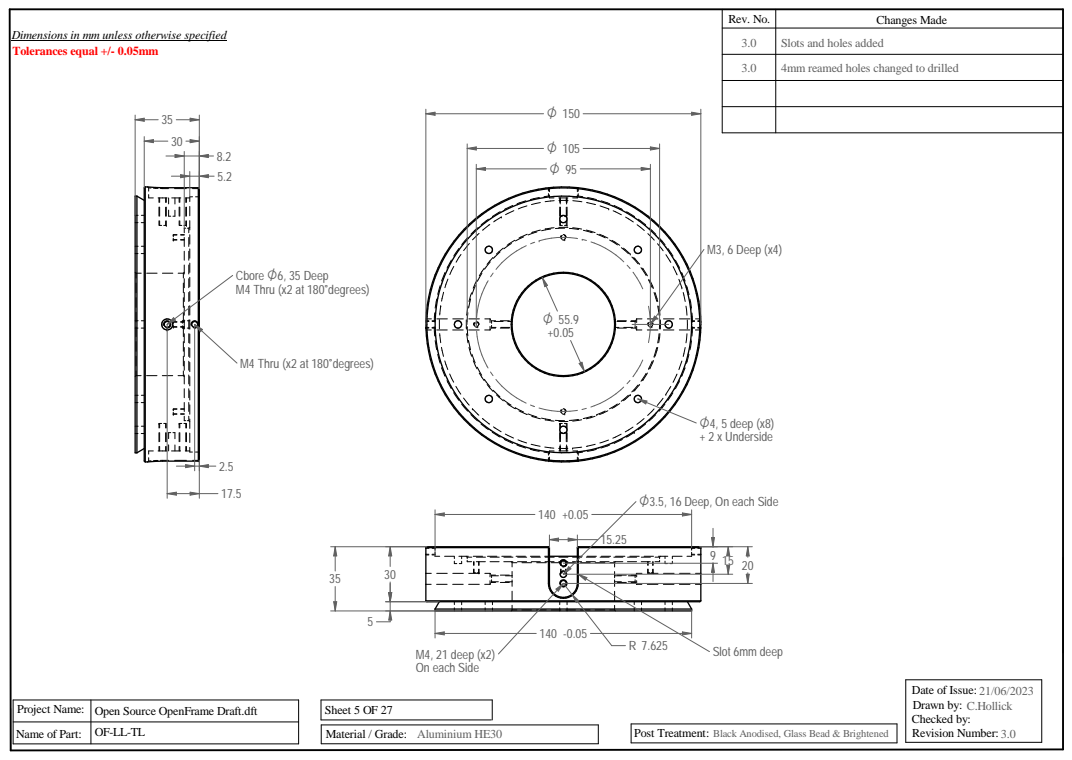
[picture p61: page 1]
Project Name:; Material / Grade:; Post Treatment:; Open Source OpenFrame Draft.dft; Sheet 5 OF 27; O4, 5 deep (x8) + 2 x Underside; Aluminium HE30; Black Anodised, Glass Bead & Brightened; C.Hollick; Cbore O6, 35 Deep M4 Thru (x2 at 180vdegrees); M3, 6 Deep (x4); Slot 6mm deep; M4 Thru (x2 at 180vdegrees)

Rev. No. | Changes Made

Dimensions in mm unless otherwise specified
Tolerances equal +/- 0.05mm

3.0 | Slots and holes added

3.0 | 4mm reamed holes changed to drilled

O3.5, 16 Deep, On each Side

M4, 21 deep (x2)
On each Side

Date of Issue:
Drawn by:
Checked by:
Revision Number:

Name of Part:
