ImperialCollegeLondon/openFrame/openFrame part description PDFs/OF-PP-SM2.pdf

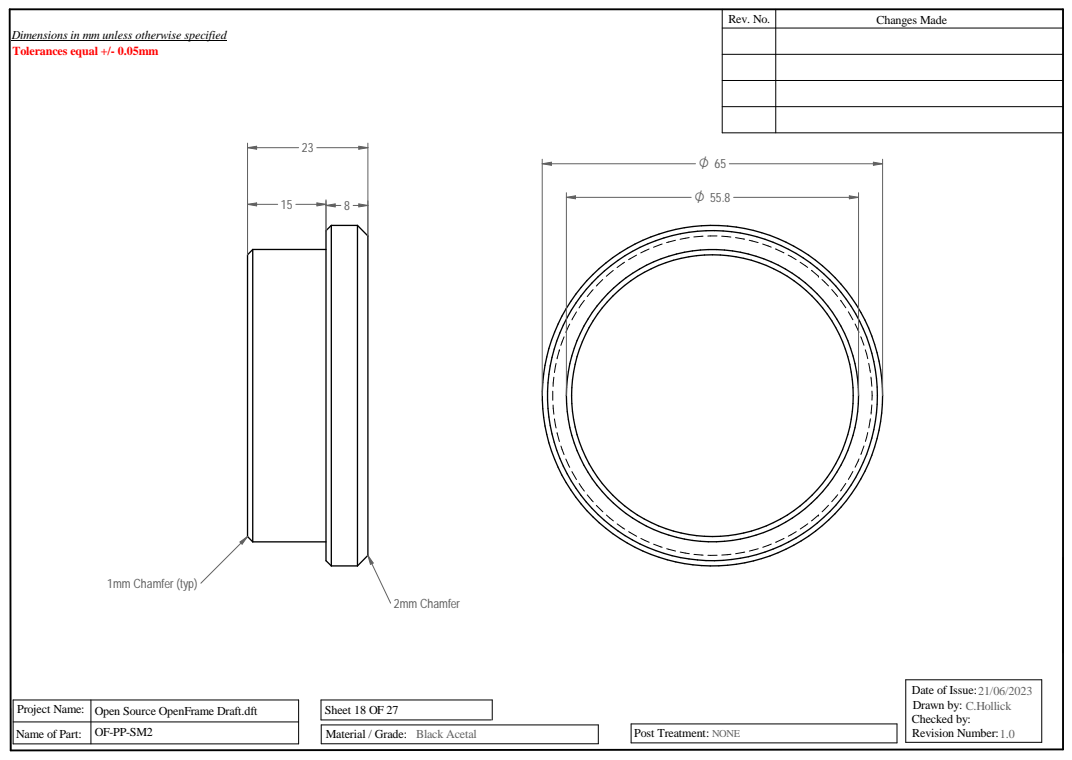
[picture p62: page 1]
Project Name:; Material / Grade:; Post Treatment:; Open Source OpenFrame Draft.dft; Sheet 18 OF 27; Rev. No.; Changes Made; 1mm Chamfer (typ); 2mm Chamfer; Black Acetal; NONE; C.Hollick

Dimensions in mm unless otherwise specified
Tolerances equal +/- 0.05mm

Date of Issue:
Drawn by:
Checked by:
Revision Number:

Name of Part:
