ImperialCollegeLondon/openFrame/openFrame part description PDFs/OF-PP-SM30.pdf

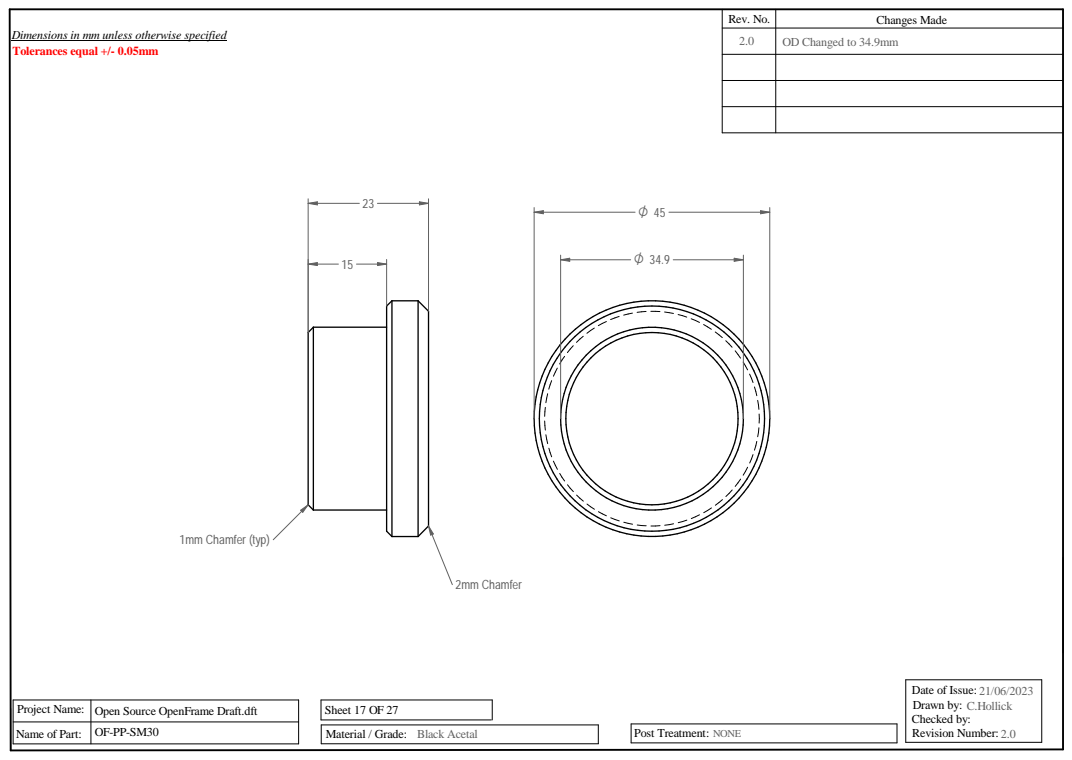
[picture p63: page 1]
Project Name:; Material / Grade:; Post Treatment:; Open Source OpenFrame Draft.dft; Sheet 17 OF 27; 1mm Chamfer (typ); 2mm Chamfer; Black Acetal; NONE; C.Hollick

Rev. No. | Changes Made

Dimensions in mm unless otherwise specified
Tolerances equal +/- 0.05mm

2.0 | OD Changed to 34.9mm

Date of Issue:
Drawn by:
Checked by:
Revision Number:

Name of Part:
